lindoran/HBKD-81/Pictures/5v DC-DC Buck Converter Module.jpg

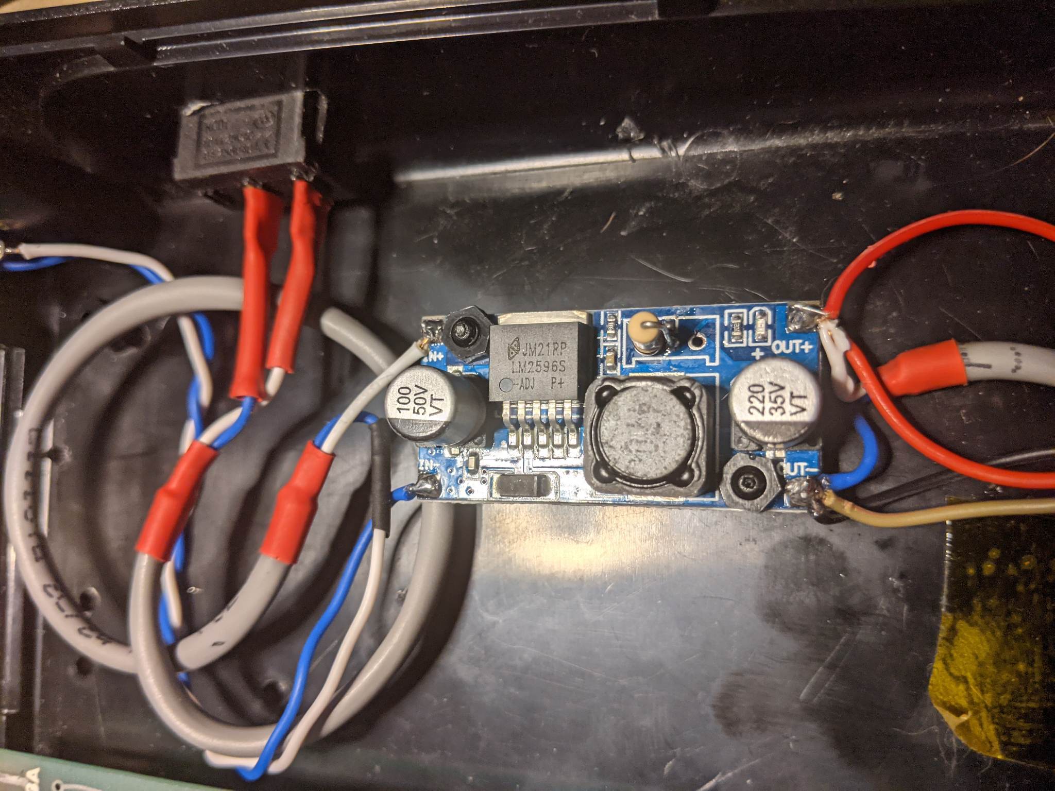
Pictures/5v DC-DC Buck Converter Module.jpg
