lindoran/HBKD-81/Pictures/back view.jpg

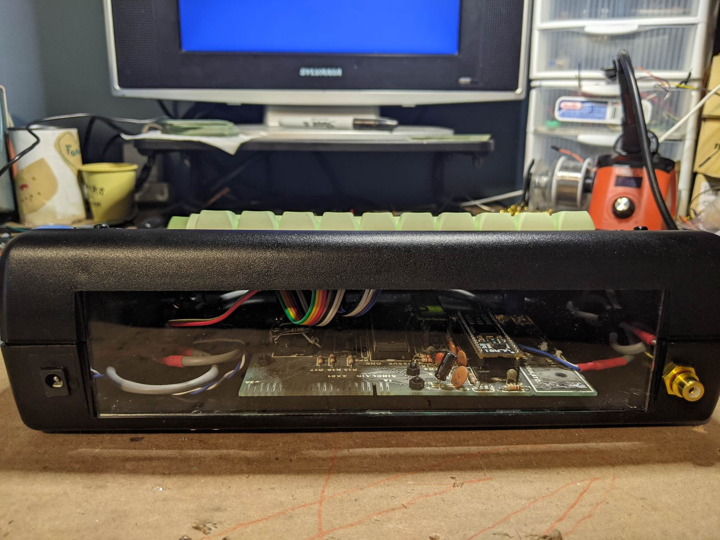
Pictures/back view.jpg
