lindoran/HBKD-81/Pictures/dc offset removal cap ⁄ video output.jpg

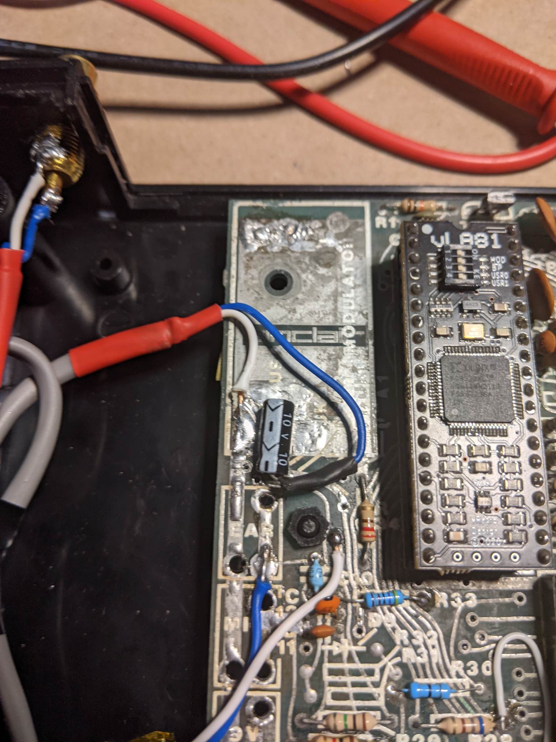
Pictures/dc offset removal cap ⁄ video output.jpg
