lindoran/HBKD-81/Pictures/Hello there.jpg

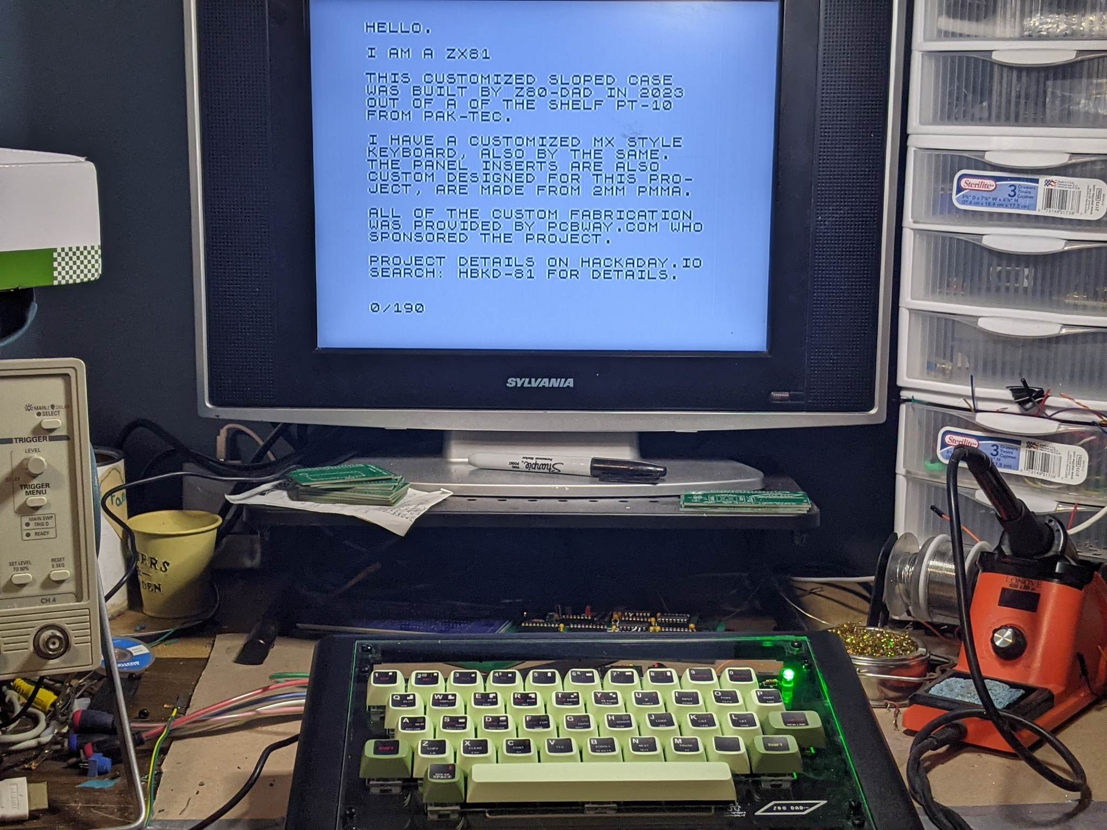
Pictures/Hello there.jpg
