lindoran/HBKD-81/Pictures/it just works.png

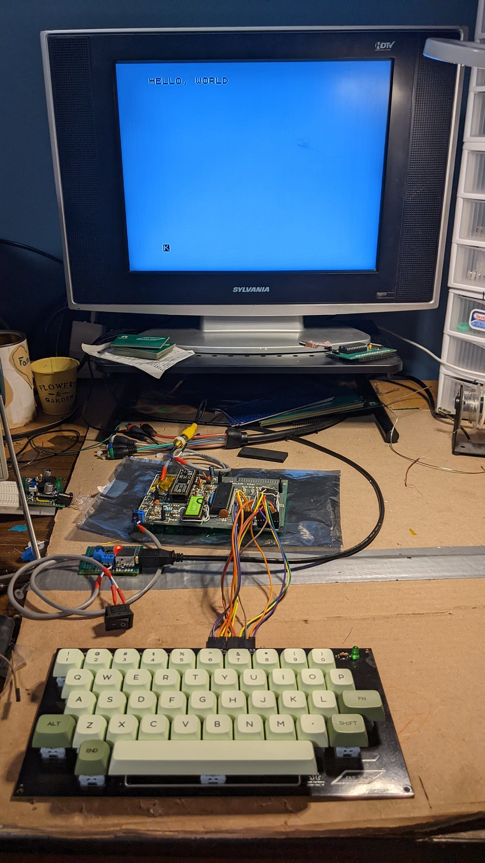
Pictures/it just works.png
