lindoran/HBKD-81/Pictures/power port w⁄ bezel cover vynal.jpg

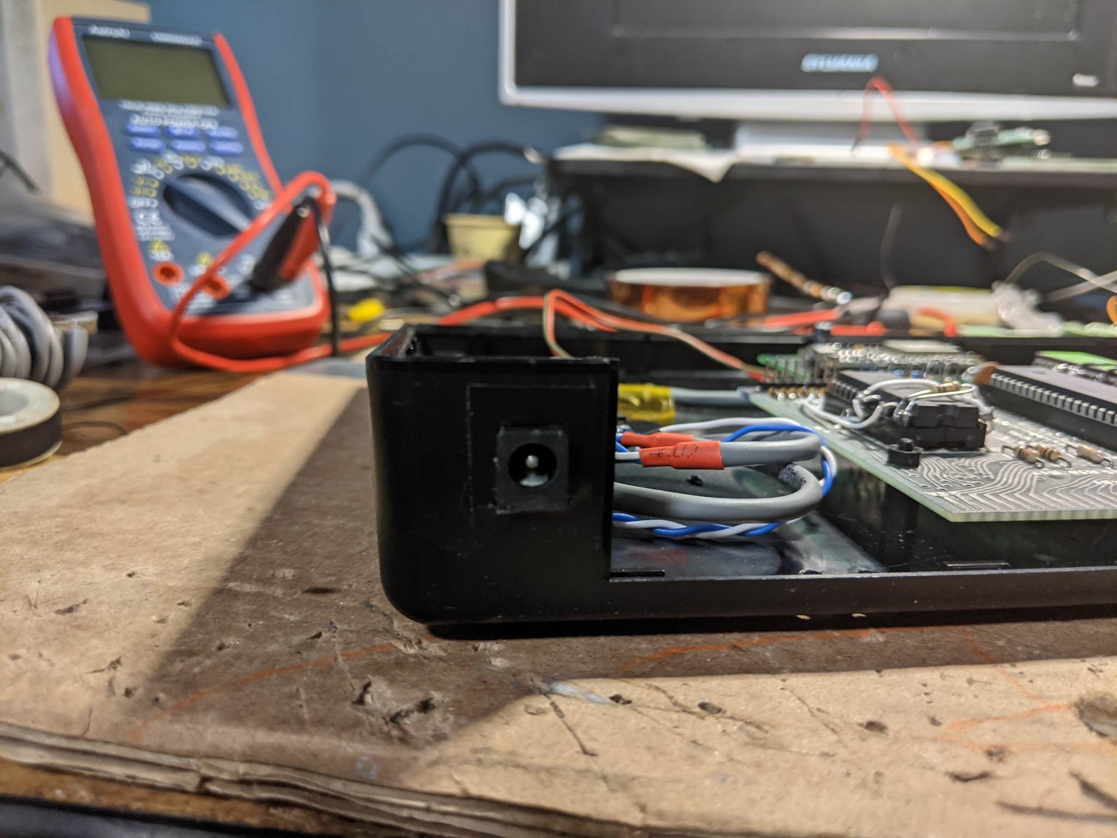
Pictures/power port w⁄ bezel cover vynal.jpg
