lindoran/HBKD-81/Pictures/power switch.jpg

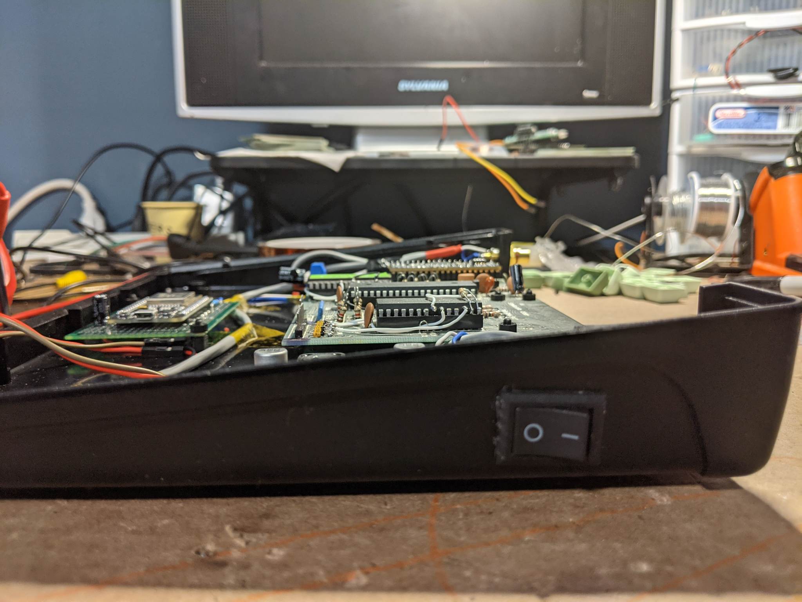
Pictures/power switch.jpg
