lindoran/HBKD-81/Pictures/tetris.jpg

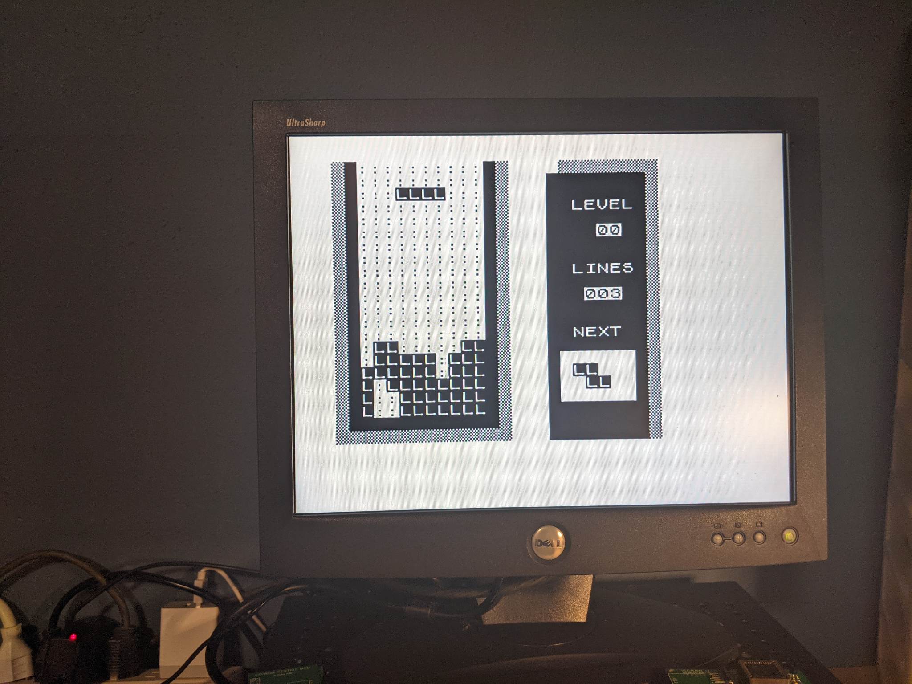
Pictures/tetris.jpg
