lindoran/HBKD-81/Pictures/tron shot #1.jpg

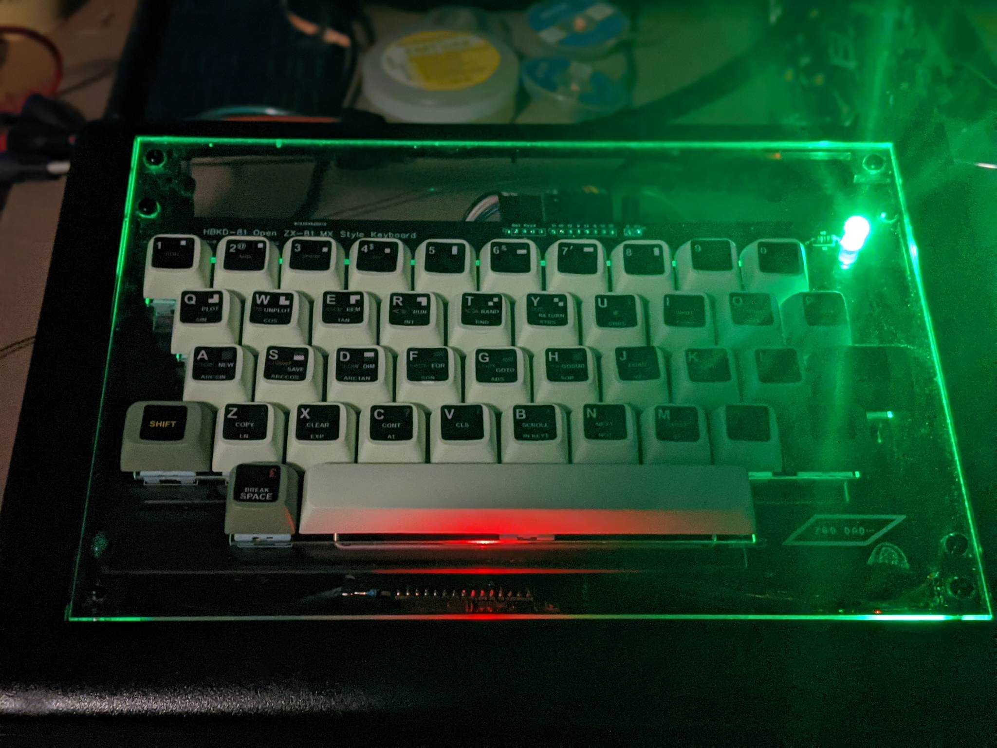
Pictures/tron shot #1.jpg
