lindoran/HBKD-81/Pictures/tron shot #2.jpg

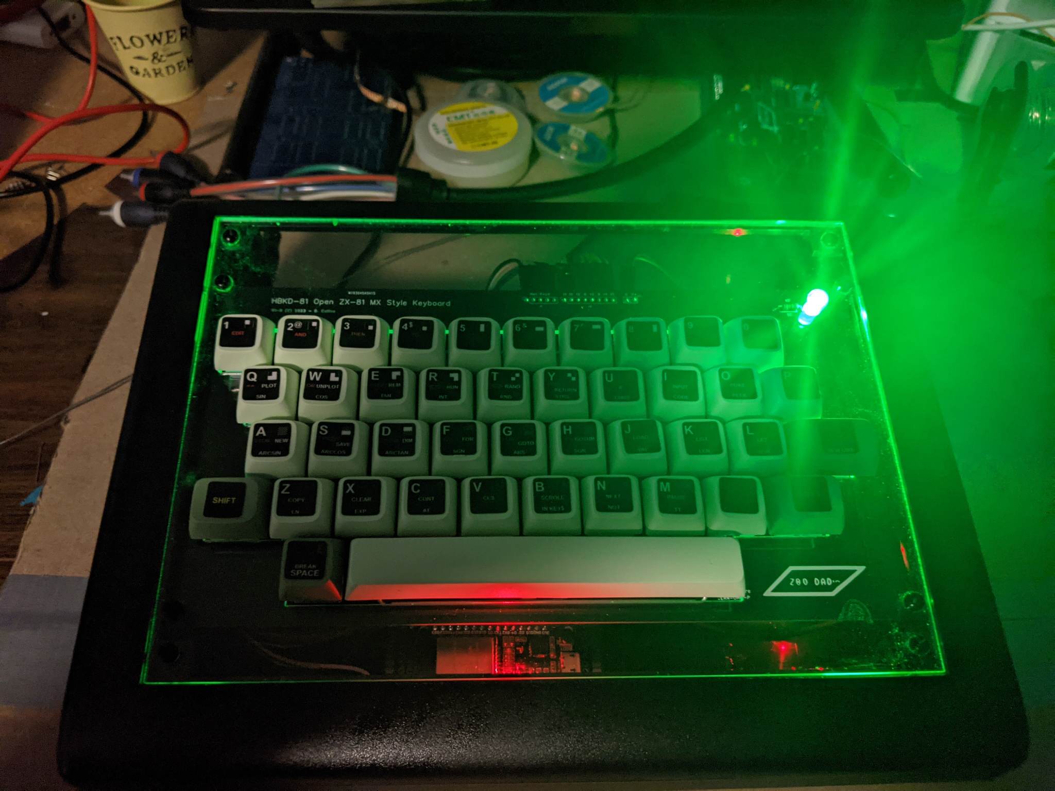
Pictures/tron shot #2.jpg
