lindoran/HBKD-81/Renders/3D_hb81_2023-03-09.png

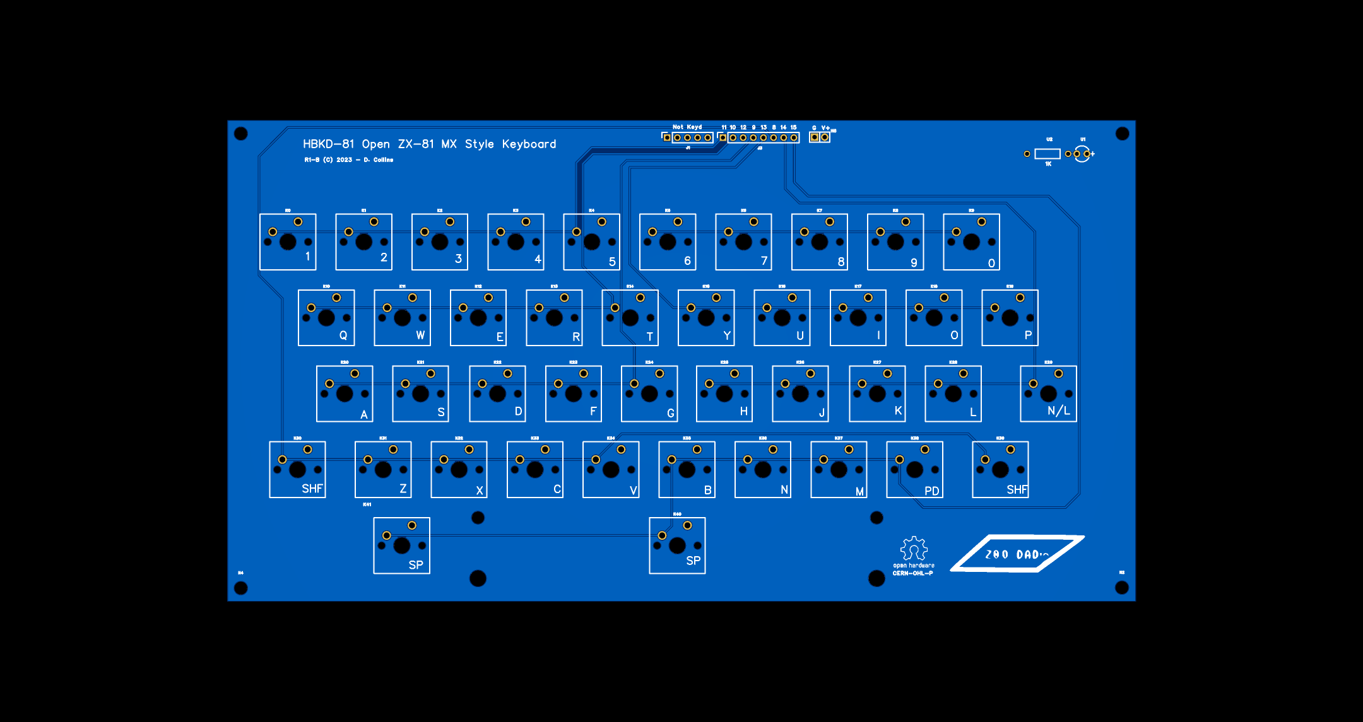
Renders/3D_hb81_2023-03-09.png
